Project-Exhale/Photobioreactor_Development/Photobioreactor/Booklet_rev2/textures/500020023-0-www-mediarath-de-smarthome-shop-d1-mini-nodemcu-esp32-wroom-wifi-iot-dev-kit-board-arduino-micro-usb-tasmota-4_1296x.webp

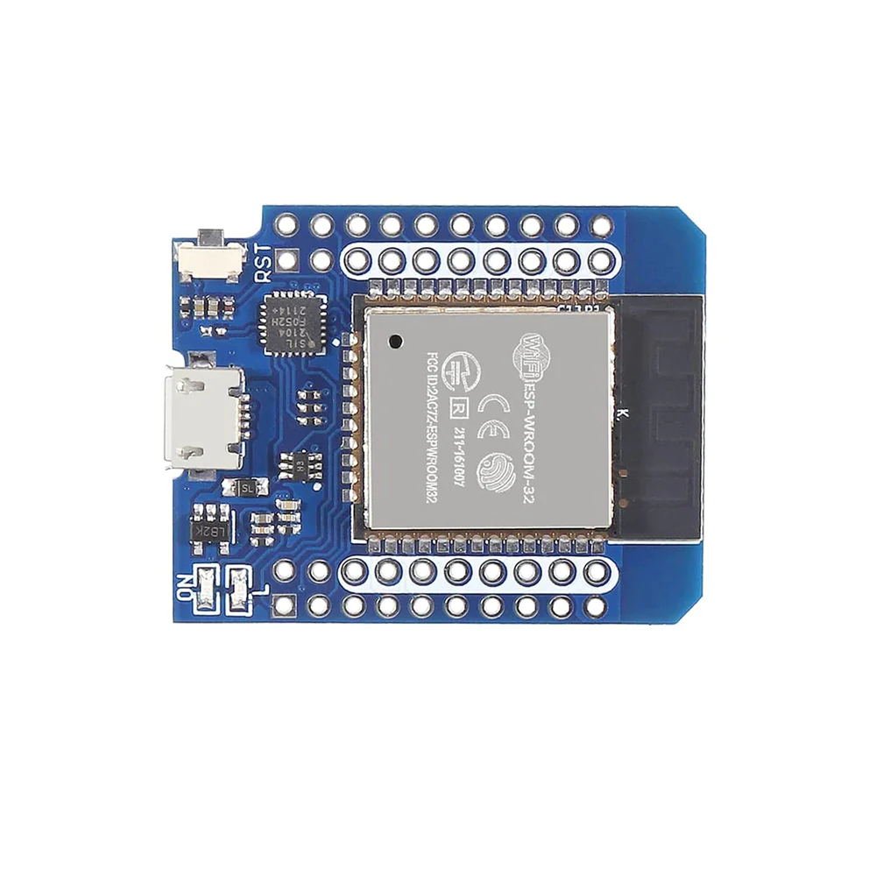
Photobioreactor/Booklet_rev2/textures/500020023-0-www-mediarath-de-smarthome-shop-d1-mini-nodemcu-esp32-wroom-wifi-iot-dev-kit-board-arduino-micro-usb-tasmota-4_1296x.webp
